Gil-gil-glitch/SudoPspsps/Images/Image 2.png

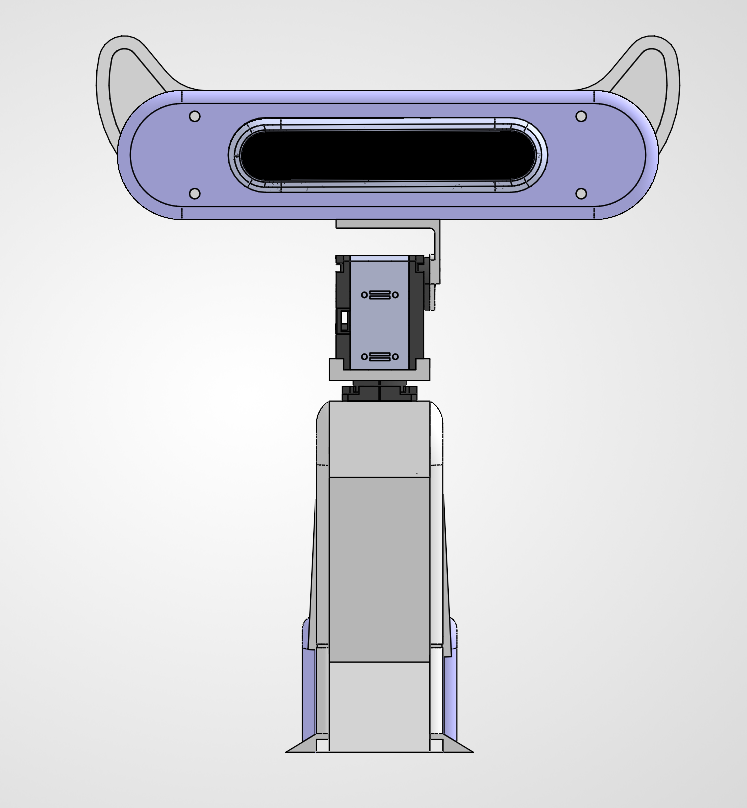
Images/Image 2.png
